turtureanu/termite-keyboard/pcb/3d-models/KS-33-Low-profile-2.0.stp

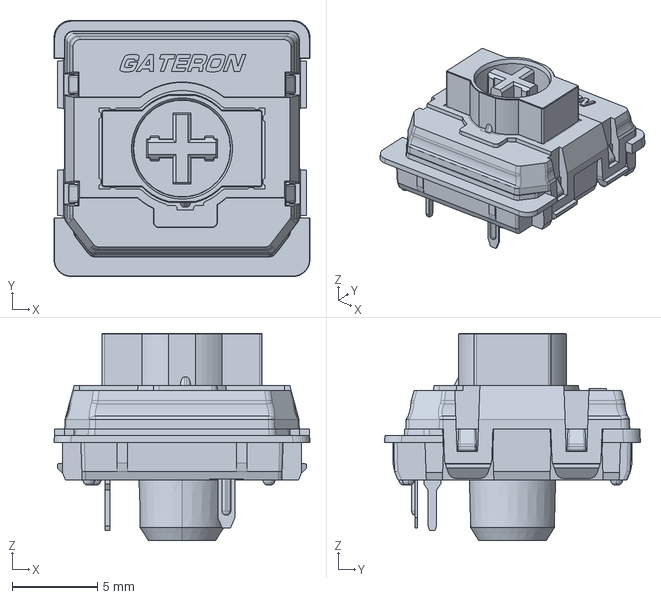
[picture p23: CAD file, 2025-04-05]
pcb/3d-models/KS-33-Low-profile-2.0.stp
15.0 x 15.0 x 12.1 mm
